Re-Yslr/AI---ESP32C3/main/led/circular_strip.cc

#include "circular_strip.h"
#include "application.h"
#include <esp_log.h>
#include <algorithm>

#define TAG "CircularStrip"

#define BLINK_INFINITE -1

CircularStrip::CircularStrip(gpio_num_t gpio, uint16_t max_leds) : max_leds_(max_leds) {
    // If the gpio is not connected, you should use NoLed class
    assert(gpio != GPIO_NUM_NC);

    colors_.resize(max_leds_);

    led_strip_config_t strip_config = {};
    strip_config.strip_gpio_num = gpio;
    strip_config.max_leds = max_leds_;
    strip_config.color_component_format = LED_STRIP_COLOR_COMPONENT_FMT_GRB;
    strip_config.led_model = LED_MODEL_WS2812;

    led_strip_rmt_config_t rmt_config = {};
    rmt_config.resolution_hz = 10 * 1000 * 1000; // 10MHz

    ESP_ERROR_CHECK(led_strip_new_rmt_device(&strip_config, &rmt_config, &led_strip_));
    led_strip_clear(led_strip_);

    esp_timer_create_args_t strip_timer_args = {
        .callback = [](void *arg) {
            auto strip = static_cast<CircularStrip*>(arg);
            std::lock_guard<std::mutex> lock(strip->mutex_);
            if (strip->strip_callback_ != nullptr) {
                strip->strip_callback_();
            }
        },
        .arg = this,
        .dispatch_method = ESP_TIMER_TASK,
        .name = "strip_timer",
        .skip_unhandled_events = false,
    };
    ESP_ERROR_CHECK(esp_timer_create(&strip_timer_args, &strip_timer_));
}

CircularStrip::~CircularStrip() {
    esp_timer_stop(strip_timer_);
    if (led_strip_ != nullptr) {
        led_strip_del(led_strip_);
    }
}


void CircularStrip::SetAllColor(StripColor color) {
    std::lock_guard<std::mutex> lock(mutex_);
    esp_timer_stop(strip_timer_);
    for (int i = 0; i < max_leds_; i++) {
        colors_[i] = color;
        led_strip_set_pixel(led_strip_, i, color.red, color.green, color.blue);
    }
    led_strip_refresh(led_strip_);
}

void CircularStrip::SetSingleColor(uint8_t index, StripColor color) {
    std::lock_guard<std::mutex> lock(mutex_);
    esp_timer_stop(strip_timer_);
    colors_[index] = color;
    led_strip_set_pixel(led_strip_, index, color.red, color.green, color.blue);
    led_strip_refresh(led_strip_);
}

void CircularStrip::SetMultiColors(const std::vector<StripColor>& colors) {
    std::lock_guard<std::mutex> lock(mutex_);
    esp_timer_stop(strip_timer_);
    int count = std::min(max_leds_, static_cast<int>(colors.size()));
    for (int i = 0; i < count; i++) {
        colors_[i] = colors[i];
        led_strip_set_pixel(led_strip_, i, colors[i].red, colors[i].green, colors[i].blue);
    }
    led_strip_refresh(led_strip_);
}

void CircularStrip::Blink(StripColor color, int interval_ms) {
    for (int i = 0; i < max_leds_; i++) {
        colors_[i] = color;
    }
    // 初始化闪烁状态
    blink_on_ = true;
    StartStripTask(interval_ms, [this]() {
        if (blink_on_) {
            for (int i = 0; i < max_leds_; i++) {
                led_strip_set_pixel(led_strip_, i, colors_[i].red, colors_[i].green, colors_[i].blue);
            }
            led_strip_refresh(led_strip_);
        } else {
            led_strip_clear(led_strip_);
        }
        blink_on_ = !blink_on_;
    });
}

void CircularStrip::FadeOut(int interval_ms) {
    StartStripTask(interval_ms, [this]() {
        bool all_off = true;
        for (int i = 0; i < max_leds_; i++) {
            colors_[i].red /= 2;
            colors_[i].green /= 2;
            colors_[i].blue /= 2;
            if (colors_[i].red != 0 || colors_[i].green != 0 || colors_[i].blue != 0) {
                all_off = false;
            }
            led_strip_set_pixel(led_strip_, i, colors_[i].red, colors_[i].green, colors_[i].blue);
        }
        if (all_off) {
            led_strip_clear(led_strip_);
            esp_timer_stop(strip_timer_);
        } else {
            led_strip_refresh(led_strip_);
        }
    });
}

void CircularStrip::Breathe(StripColor low, StripColor high, int interval_ms) {
    // 初始化呼吸状态（每次调用都重置，解决切换颜色后灯光变暗的问题）
    breathe_increase_ = true;
    breathe_color_ = low;
    
    StartStripTask(interval_ms, [this, low, high]() {
        if (breathe_increase_) {
            if (breathe_color_.red < high.red) {
                breathe_color_.red++;
            }
            if (breathe_color_.green < high.green) {
                breathe_color_.green++;
            }
            if (breathe_color_.blue < high.blue) {
                breathe_color_.blue++;
            }
            if (breathe_color_.red == high.red && breathe_color_.green == high.green && breathe_color_.blue == high.blue) {
                breathe_increase_ = false;
            }
        } else {
            if (breathe_color_.red > low.red) {
                breathe_color_.red--;
            }
            if (breathe_color_.green > low.green) {
                breathe_color_.green--;
            }
            if (breathe_color_.blue > low.blue) {
                breathe_color_.blue--;
            }
            if (breathe_color_.red == low.red && breathe_color_.green == low.green && breathe_color_.blue == low.blue) {
                breathe_increase_ = true;
            }
        }
        for (int i = 0; i < max_leds_; i++) {
            led_strip_set_pixel(led_strip_, i, breathe_color_.red, breathe_color_.green, breathe_color_.blue);
        }
        led_strip_refresh(led_strip_);
    });
}

void CircularStrip::Scroll(StripColor low, StripColor high, int length, int interval_ms) {
    for (int i = 0; i < max_leds_; i++) {
        colors_[i] = low;
    }
    // 初始化滚动偏移
    scroll_offset_ = 0;
    StartStripTask(interval_ms, [this, low, high, length]() {
        for (int i = 0; i < max_leds_; i++) {
            colors_[i] = low;
        }
        for (int j = 0; j < length; j++) {
            int i = (scroll_offset_ + j) % max_leds_;
            colors_[i] = high;
        }
        for (int i = 0; i < max_leds_; i++) {
            led_strip_set_pixel(led_strip_, i, colors_[i].red, colors_[i].green, colors_[i].blue);
        }
        led_strip_refresh(led_strip_);
        scroll_offset_ = (scroll_offset_ + 1) % max_leds_;
    });
}

void CircularStrip::StartStripTask(int interval_ms, std::function<void()> cb) {
    if (led_strip_ == nullptr) {
        return;
    }

    std::lock_guard<std::mutex> lock(mutex_);
    esp_timer_stop(strip_timer_);
    
    strip_callback_ = cb;
    esp_timer_start_periodic(strip_timer_, interval_ms * 1000);
}

void CircularStrip::SetBrightness(uint8_t default_brightness, uint8_t low_brightness) {
    default_brightness_ = default_brightness;
    low_brightness_ = low_brightness;
    OnStateChanged();
}

void CircularStrip::OnStateChanged() {
    auto& app = Application::GetInstance();
    auto device_state = app.GetDeviceState();
    switch (device_state) {
        case kDeviceStateStarting: {
            StripColor low = { 0, 0, 0 };
            StripColor high = { low_brightness_, low_brightness_, default_brightness_ };
            Scroll(low, high, 3, 100);
            break;
        }
        case kDeviceStateWifiConfiguring: {
            StripColor color = { low_brightness_, low_brightness_, default_brightness_ };
            Blink(color, 500);
            break;
        }
        case kDeviceStateIdle:
            FadeOut(50);
            break;
        case kDeviceStateConnecting: {
            StripColor color = { low_brightness_, low_brightness_, default_brightness_ };
            SetAllColor(color);
            break;
        }
        case kDeviceStateListening:
        case kDeviceStateAudioTesting: {
            StripColor color = { default_brightness_, low_brightness_, low_brightness_ };
            SetAllColor(color);
            break;
        }
        case kDeviceStateSpeaking: {
            StripColor color = { low_brightness_, default_brightness_, low_brightness_ };
            SetAllColor(color);
            break;
        }
        case kDeviceStateUpgrading: {
            StripColor color = { low_brightness_, default_brightness_, low_brightness_ };
            Blink(color, 100);
            break;
        }
        case kDeviceStateActivating: {
            StripColor color = { low_brightness_, default_brightness_, low_brightness_ };
            Blink(color, 500);
            break;
        }
        default:
            ESP_LOGW(TAG, "Unknown led strip event: %d", device_state);
            return;
    }
}
